jsjolund/dmx512-controller-board/Images/kicad_pcb_lcd.png

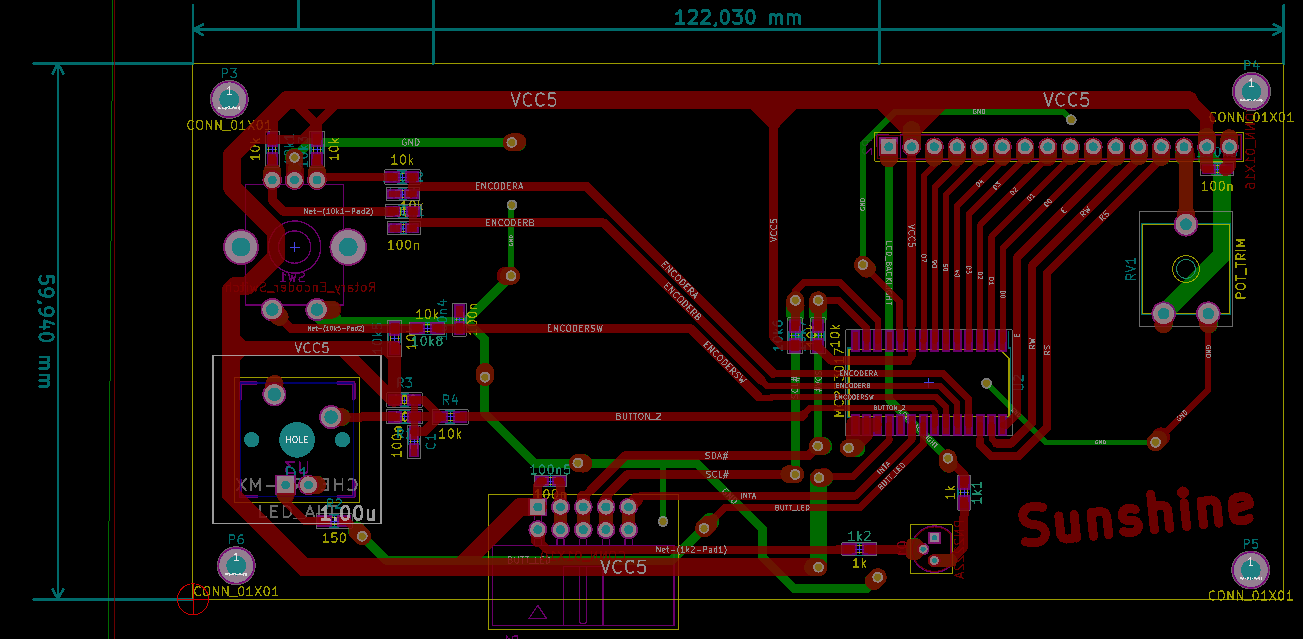
Images/kicad_pcb_lcd.png
