jsjolund/dmx512-controller-board/Images/kicad_pcb_main.png

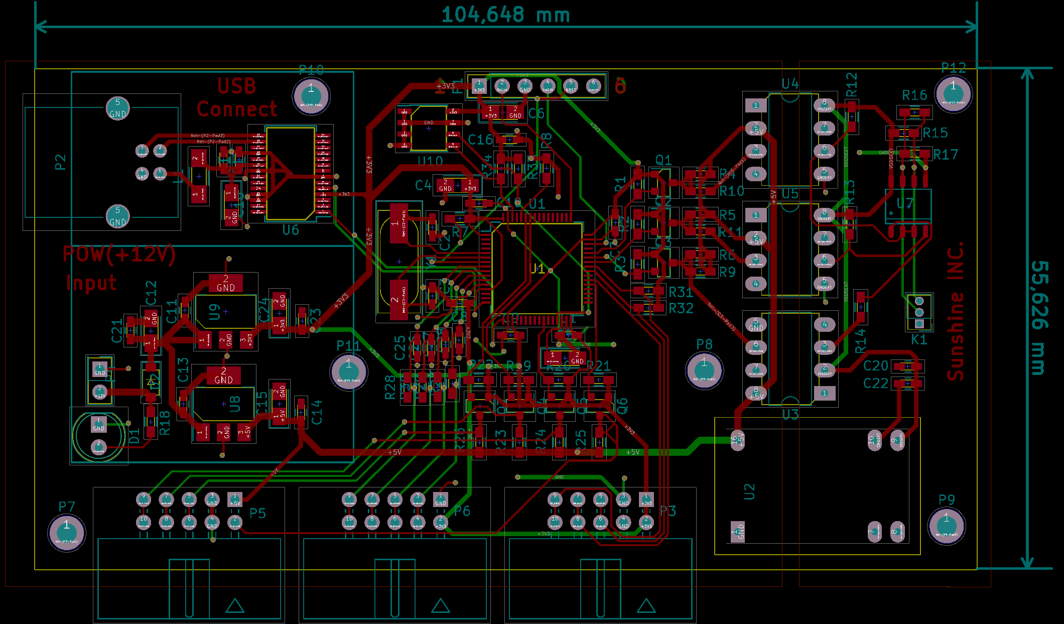
Images/kicad_pcb_main.png
