jsjolund/dmx512-controller-board/Images/used_pins.png

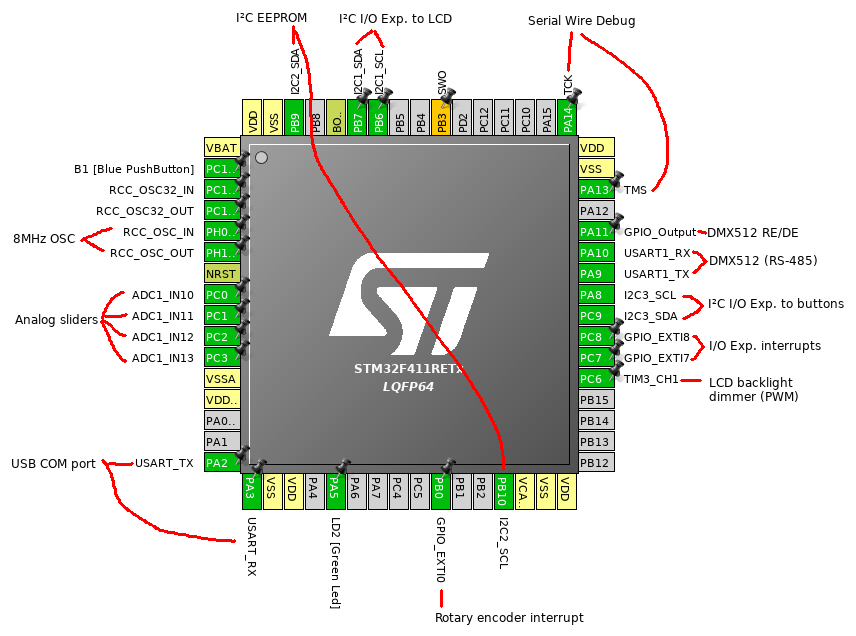
Images/used_pins.png
