jsjolund/dmx512-controller-board/Inc/shell.h

/*
 * shell.h
 *
 *  Created on: Feb 25, 2017
 *      Author: user
 */

#ifndef SHELL_H_
#define SHELL_H_

#include <stdio.h>
#include <stdlib.h>
#include <string.h>
#include "dmx512.h"
#include "lcd.h"

void ShellExecute(char* string);

#endif /* SHELL_H_ */
